dirkt68/iCEGenius/board/esp32-current/sims/inverter_test.asc

Q1: npn
R1: res; 10k
R2: res; 10k
V1: voltage; 3.3
V2: voltage; 0
Named nets: 0, VDD, INPUT, CRESET_B
