dirkt68/iCEGenius/board/esp32-current/sims/Draft4.asc

M1: pmos; BSS84
Q1: npn; 2N3904
R1: res; 10k
R2: res; 10k
R3: res; 10k
R4: res; 10k
V1: voltage; 3.6
V2: voltage; 3.6
Named nets: 0, Vout, Vbatt
.tran 0 1 0
