dirkt68/iCEGenius/board/esp32-current/sims/Draft1.asc

R1: res; 1Meg
R2: res; 1.5Meg
V1: voltage; 3.3
Named nets: 0, VCC, Vout
