dirkt68/iCEGenius/board/esp32-current/sims/Draft2.asc

M1: nmos; AONS66641
R1: res; 10k
R2: res; 10k
R3: res; 10k
V1: voltage; 3.6
V2: voltage; 3.3
Named nets: 0, Vin, OnOff, Vout
.tran 0 1 0 .01
