dirkt68/iCEGenius/board/esp32-current/sims/Draft3.asc

M1: pmos; AO6407
Q2: npn; BC547B
R1: res; 10k
R2: res; 10k
R3: res; 10k
R4: res; 10k
R5: res; 10k
V1: voltage; 3.3
V2: voltage; 0
Named nets: 0, Vin, Vout
.tran 0 10 0
