dirkt68/iCEGenius/extension/src/test/leds/leds.pcf

set_io LED4 1
set_io LED3 2
set_io LED2 5
set_io LED1 6
set_io LED0 7
