dirkt68/iCEGenius/extension/src/test/leds/src/leds.v

`timescale 1ns/1ps

module leds(output wire LED0,
            output wire LED1,
            output wire LED2,
            output wire LED3,
            output wire LED4);


assign LED0 = 1;
assign LED1 = 0;
assign LED2 = 1;
assign LED3 = 0;
assign LED4 = 1;

endmodule
